OJessup/LightsaberAntimatter/DocsAndDiagrams/V2.0/Lightsaber [Antimatter] Block Diagram V2.0.jpeg

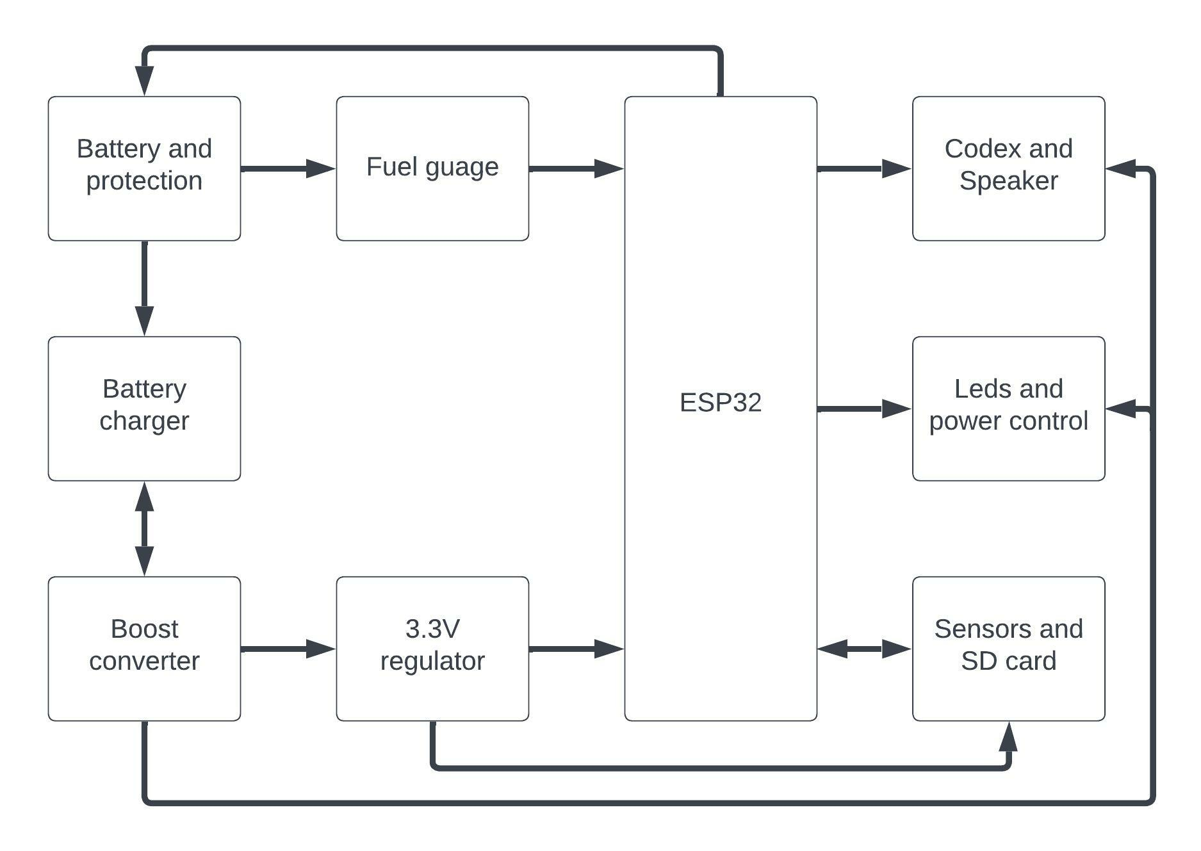
DocsAndDiagrams/V2.0/Lightsaber [Antimatter] Block Diagram V2.0.jpeg
