OJessup/LightsaberAntimatter/Inspiration/Copper and aluminium.jpeg

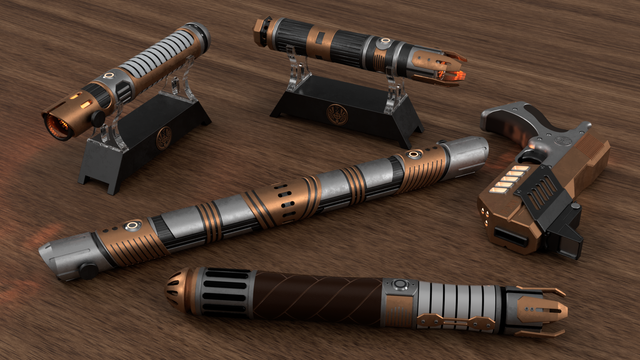
Inspiration/Copper and aluminium.jpeg
