OJessup/LightsaberAntimatter/Inspiration/Gold and Black.jpeg

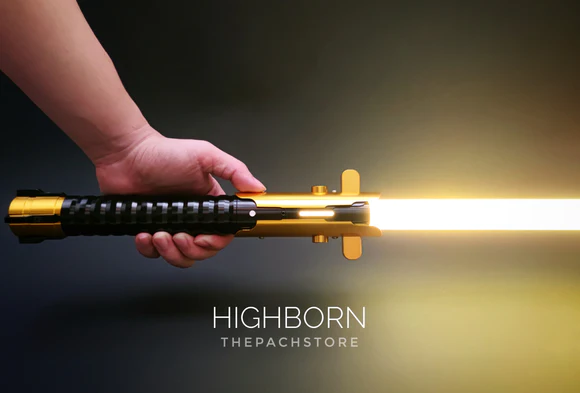
Inspiration/Gold and Black.jpeg
