OJessup/LightsaberAntimatter/Inspiration/Leather grip.jpeg

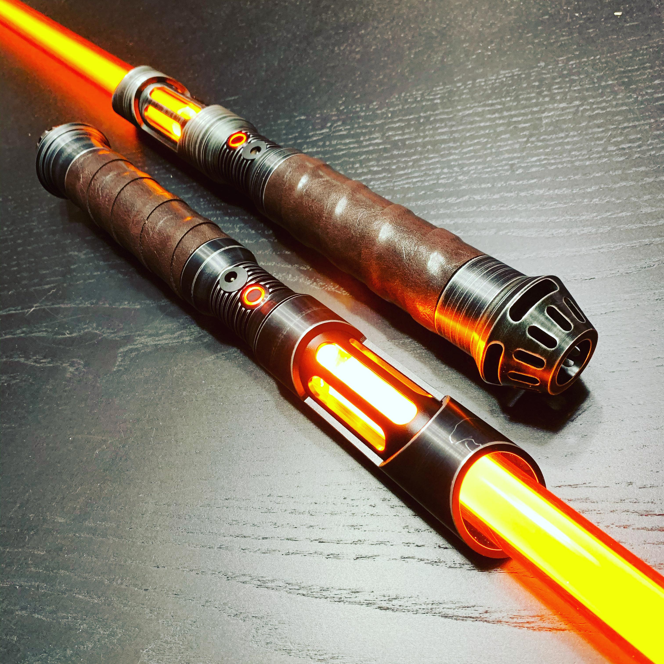
Inspiration/Leather grip.jpeg
