OJessup/LightsaberAntimatter/Inspiration/starkiller 1.jpeg

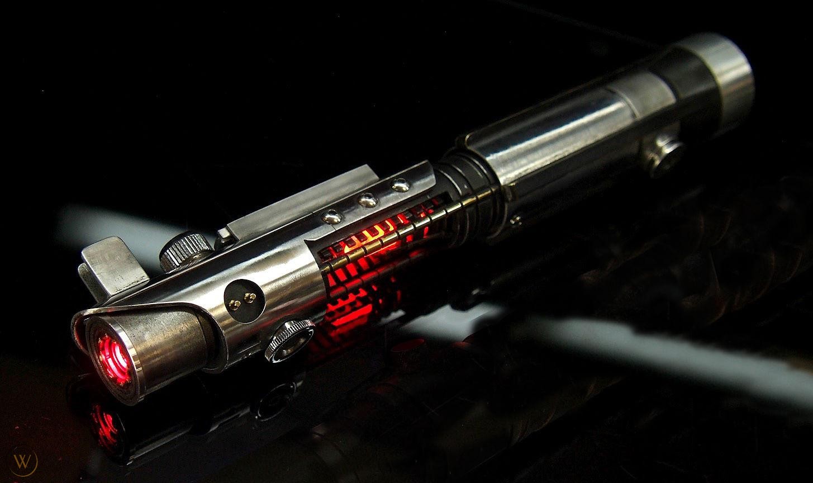
Inspiration/starkiller 1.jpeg
