OJessup/LightsaberAntimatter/Inspiration/starkiller 3.jpeg

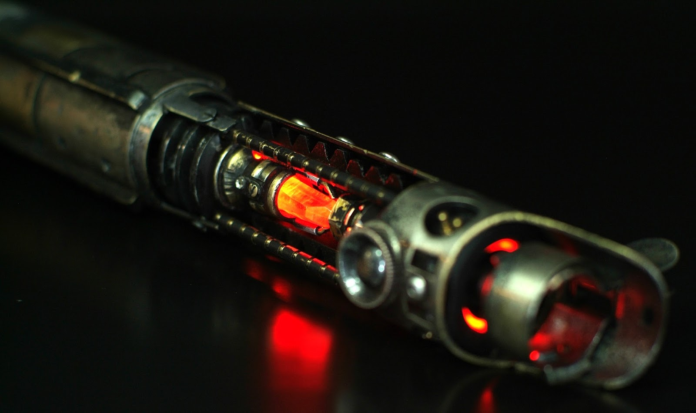
Inspiration/starkiller 3.jpeg
