OJessup/LightsaberAntimatter/Inspiration/starkiller 4.jpeg

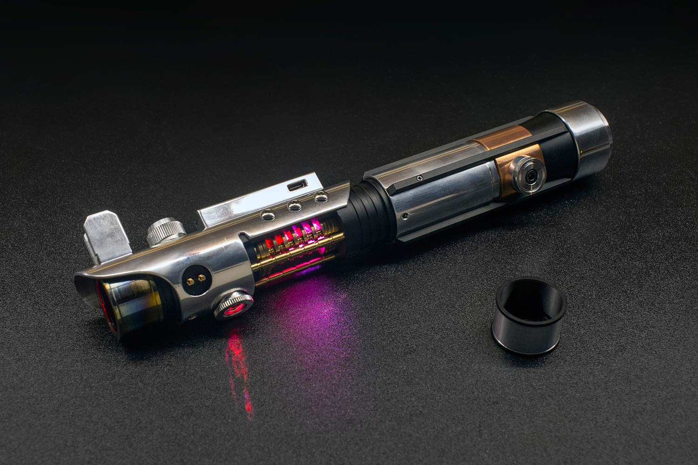
Inspiration/starkiller 4.jpeg
