OJessup/LightsaberAntimatter/ProgressDump/3A280642-E206-4C3E-A6EC-DA5A2EA1DF64.jpg

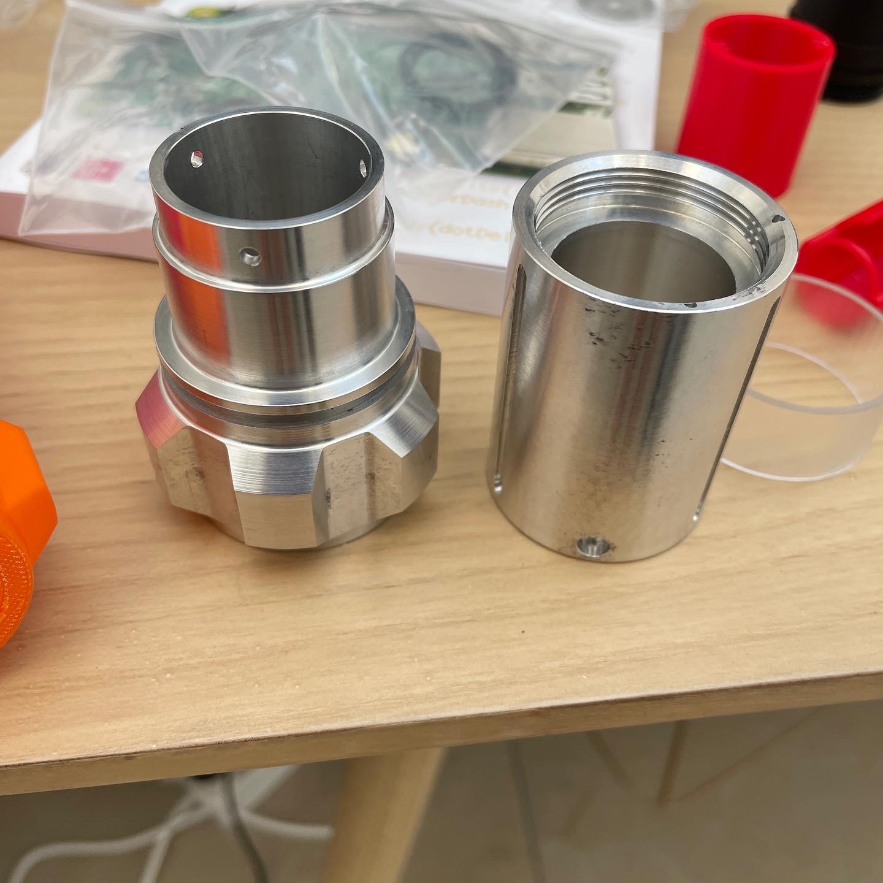
ProgressDump/3A280642-E206-4C3E-A6EC-DA5A2EA1DF64.jpg
