OJessup/LightsaberAntimatter/ProgressDump/76434946-092B-4D3E-A22C-4221BAEBB1AF.jpg

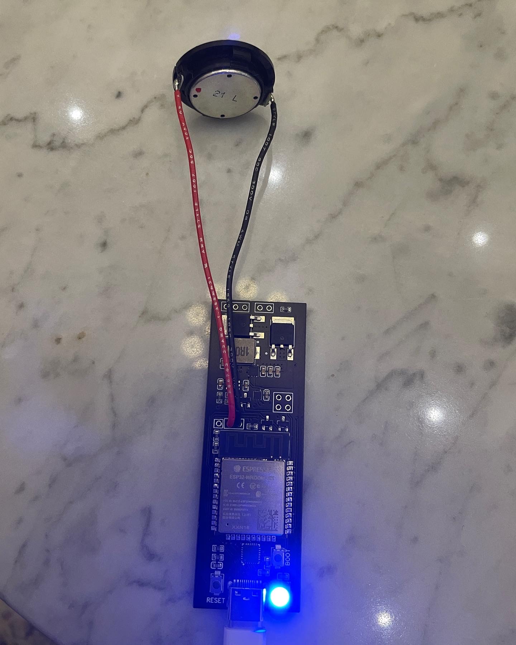
ProgressDump/76434946-092B-4D3E-A22C-4221BAEBB1AF.jpg
