OJessup/LightsaberAntimatter/ProgressDump/ABE4BEE7-62A8-4462-B97B-0894F94DCD76.jpg

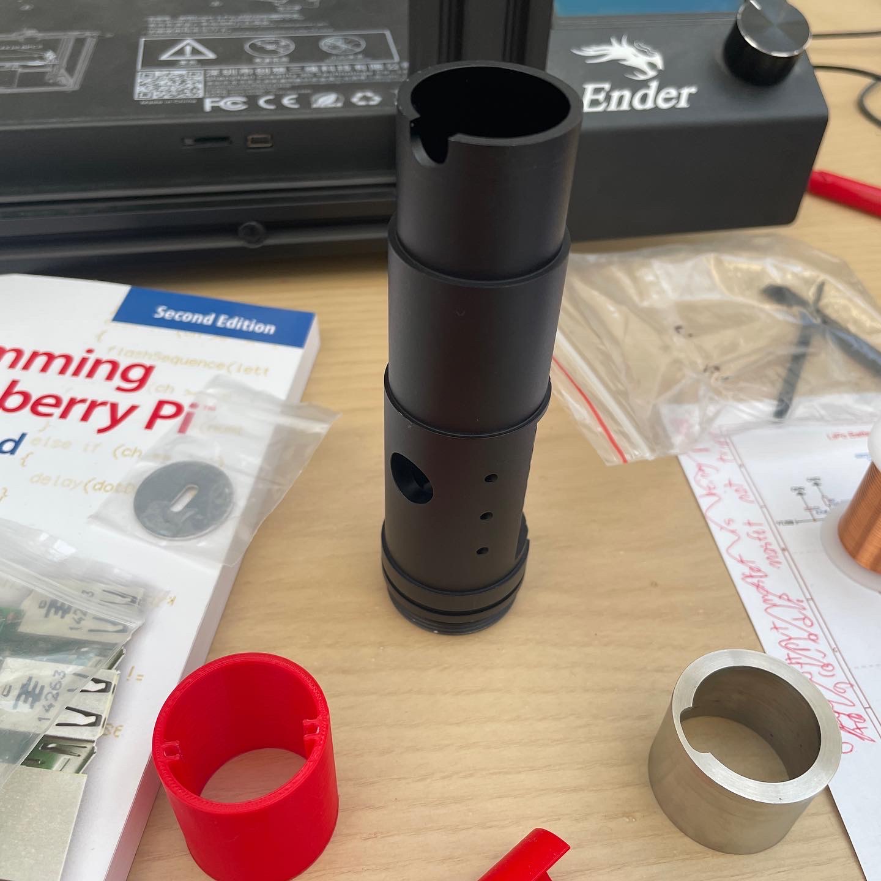
ProgressDump/ABE4BEE7-62A8-4462-B97B-0894F94DCD76.jpg
