OJessup/LightsaberAntimatter/ProgressDump/IMG_3394.JPG

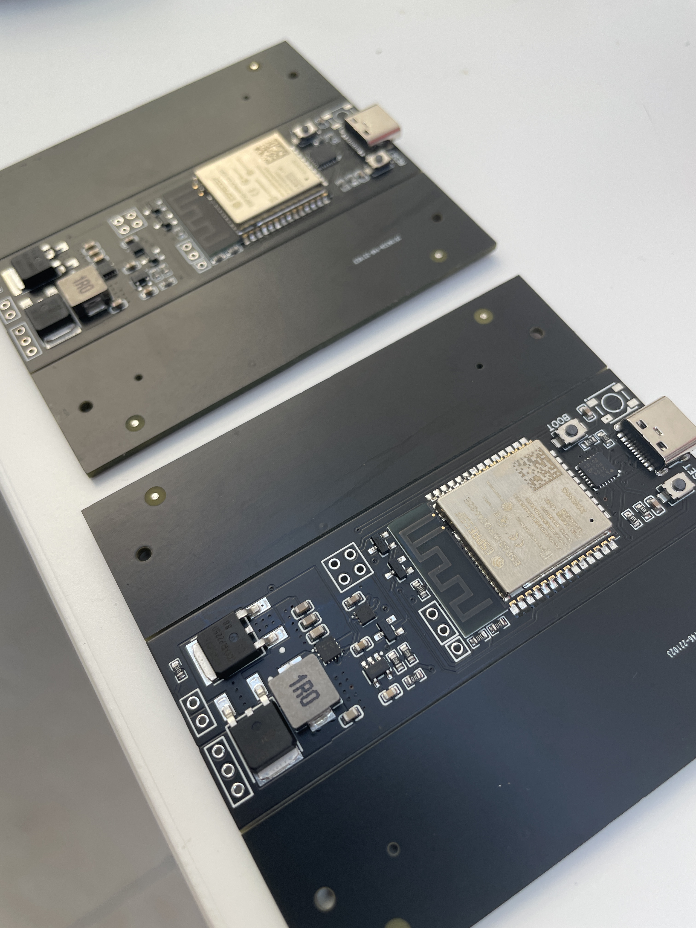
ProgressDump/IMG_3394.JPG
