OJessup/LightsaberAntimatter/ProgressDump/IMG_3398.JPG

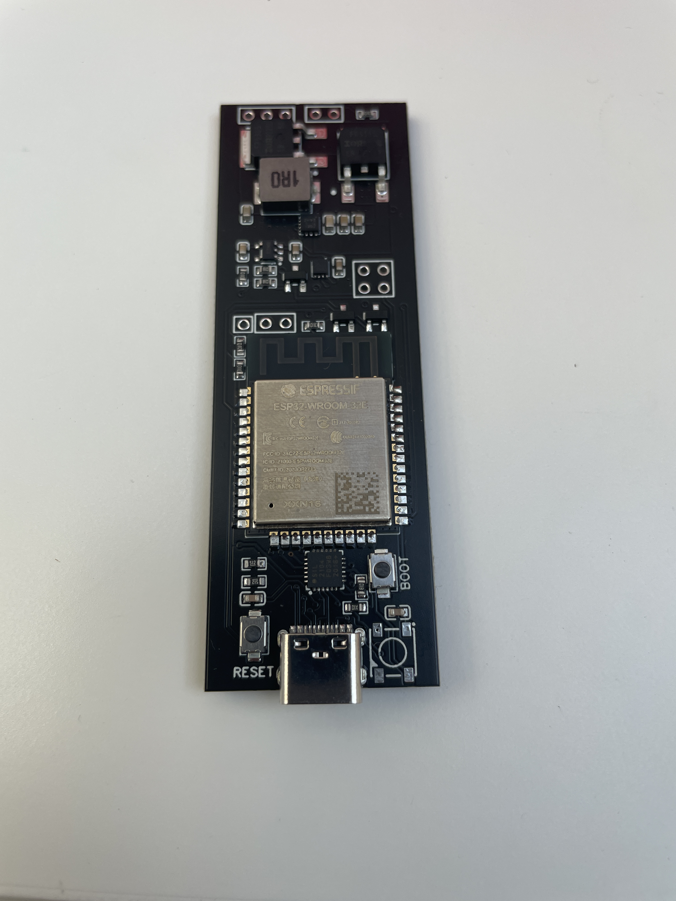
ProgressDump/IMG_3398.JPG
