OJessup/LightsaberAntimatter/ProgressDump/IMG_3399.JPG

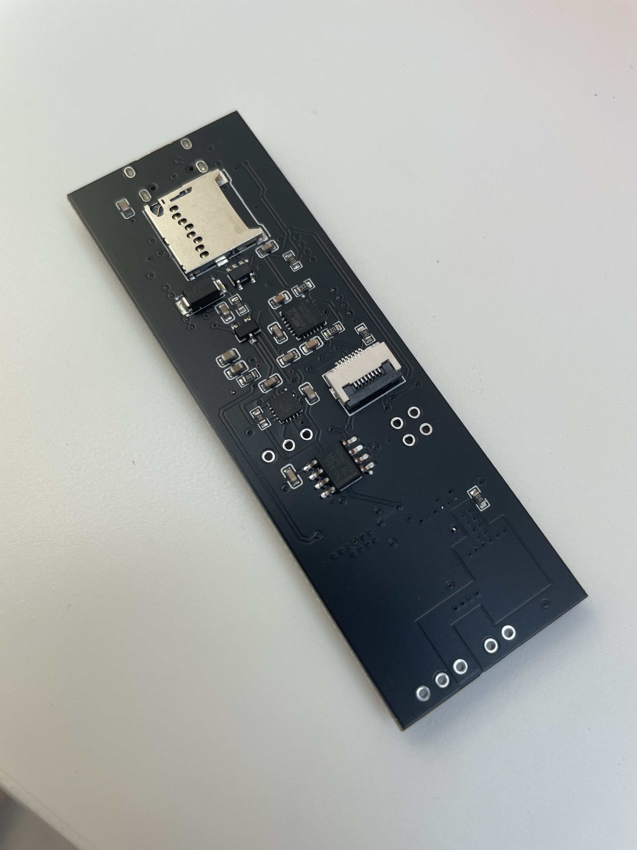
ProgressDump/IMG_3399.JPG
