OJessup/LightsaberAntimatter/ProgressDump/IMG_4058.JPG

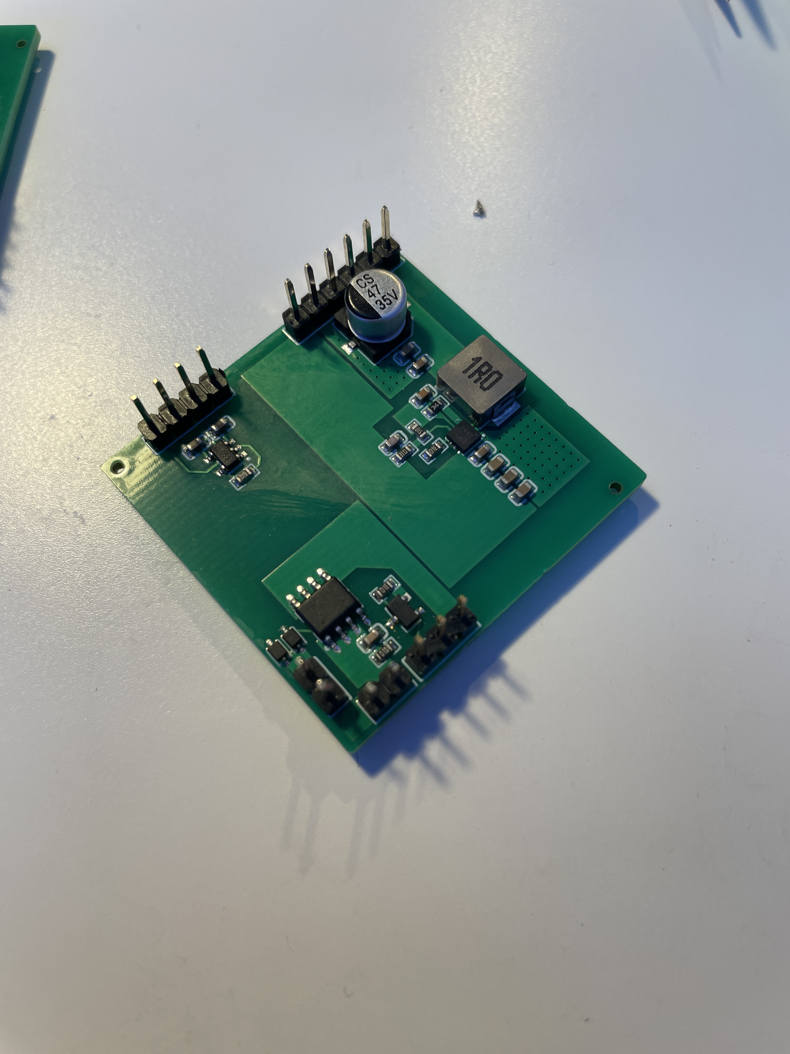
ProgressDump/IMG_4058.JPG
