OJessup/LightsaberAntimatter/ProgressDump/IMG_4652.JPG

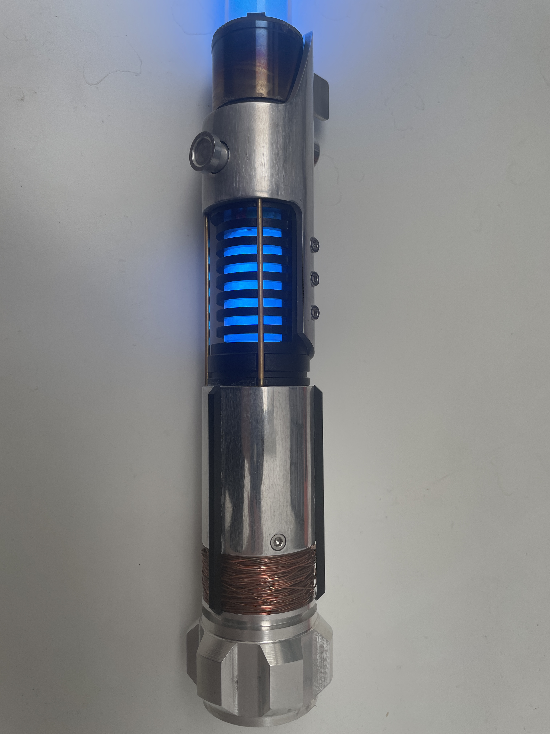
ProgressDump/IMG_4652.JPG
