OJessup/LightsaberAntimatter/CAD/STEP files/Underframe-01.step

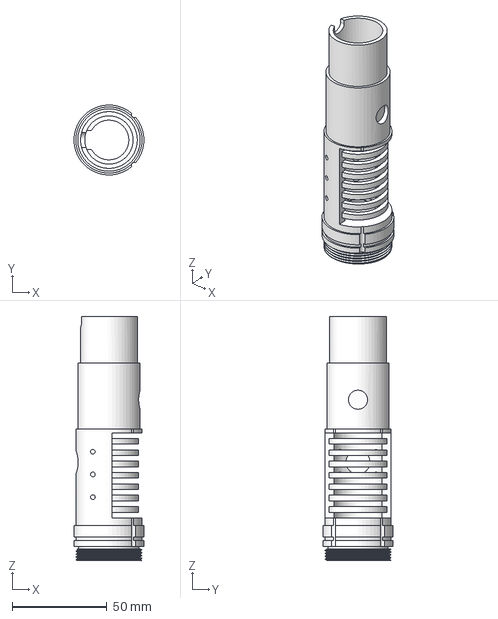
[picture p39: CAD file, 2022-11-18]
CAD/STEP files/Underframe-01.step
37.0 x 37.0 x 129.0 mm
