OJessup/LightsaberAntimatter/CAD/STEP files/EmitterCover-01.step

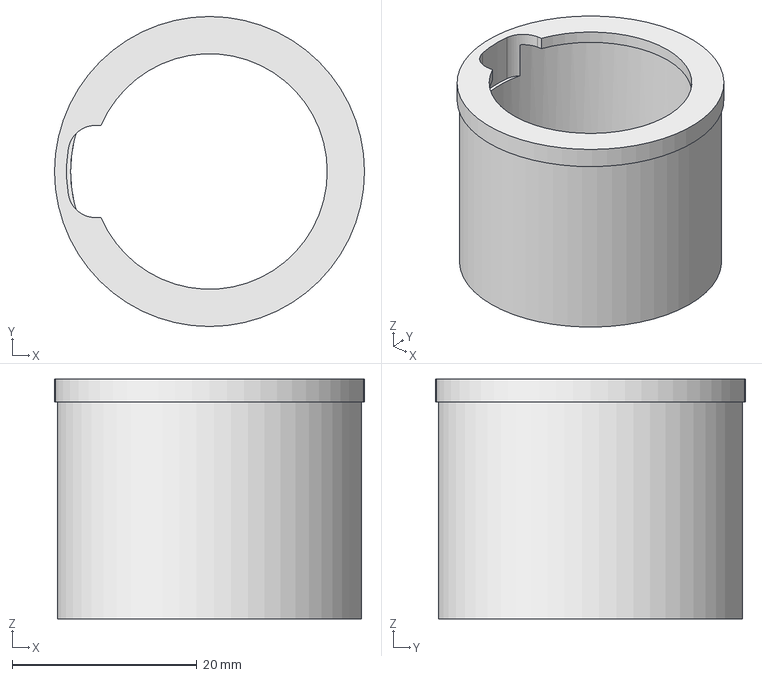
[picture p40: CAD file, 2022-11-18]
CAD/STEP files/EmitterCover-01.step
33.6 x 33.6 x 26.0 mm
