OJessup/LightsaberAntimatter/ProgressDump/IMG_3277.JPG

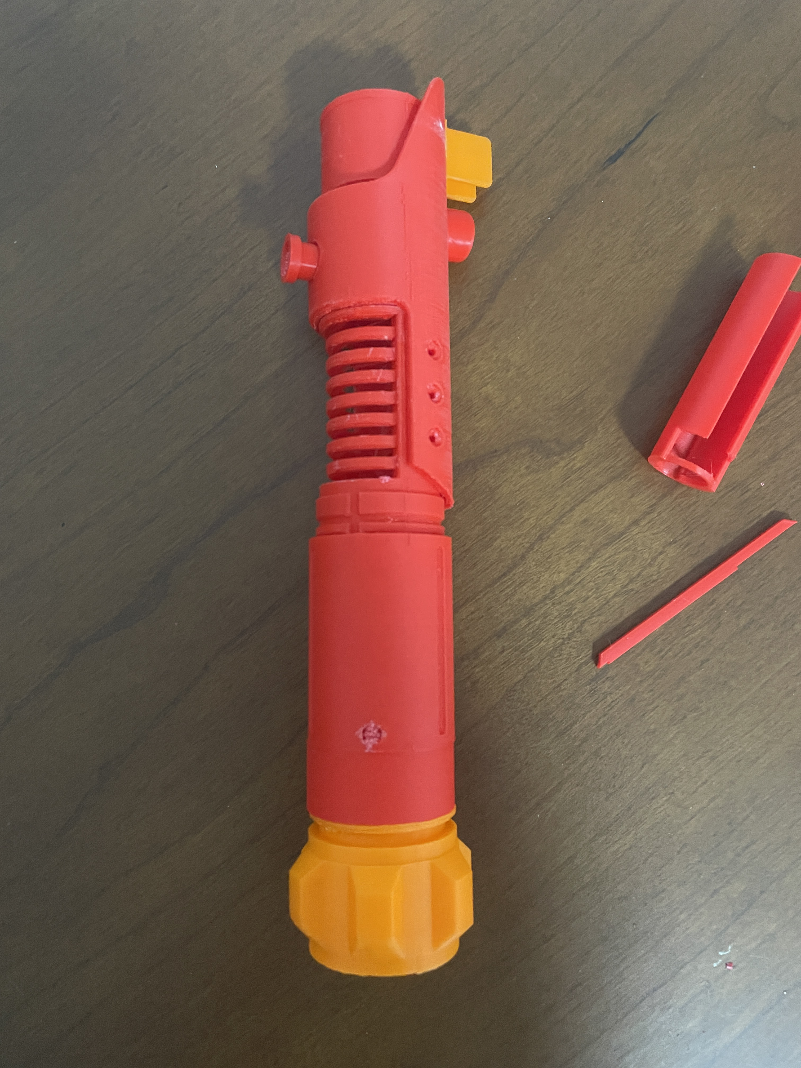
ProgressDump/IMG_3277.JPG
