OJessup/LightsaberAntimatter/ProgressDump/IMG_3279.JPG

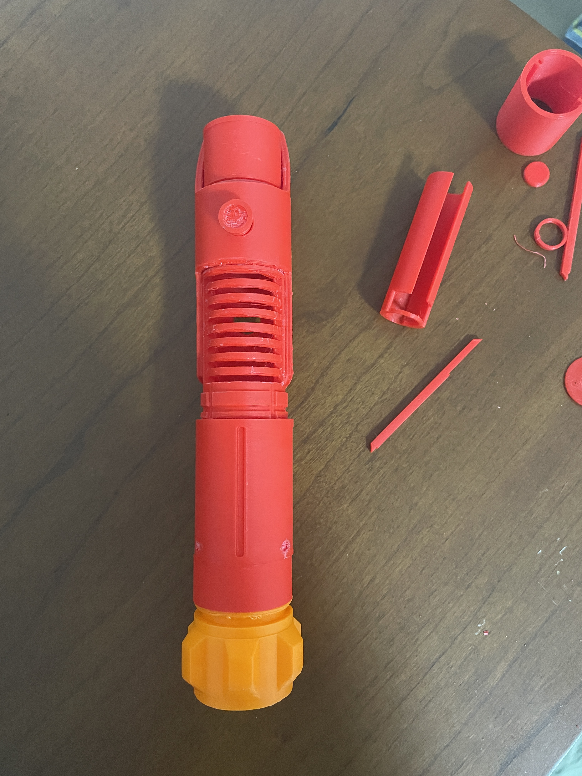
ProgressDump/IMG_3279.JPG
