OJessup/LightsaberAntimatter/ProgressDump/IMG_3930.JPG

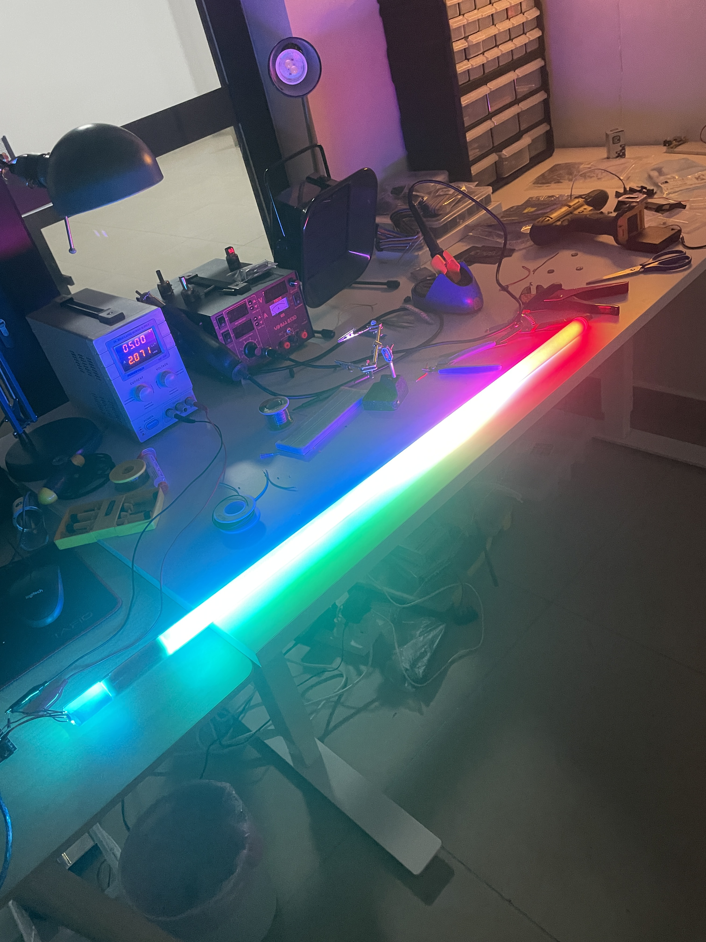
ProgressDump/IMG_3930.JPG
