OJessup/LightsaberAntimatter/ProgressDump/IMG_3598.JPG

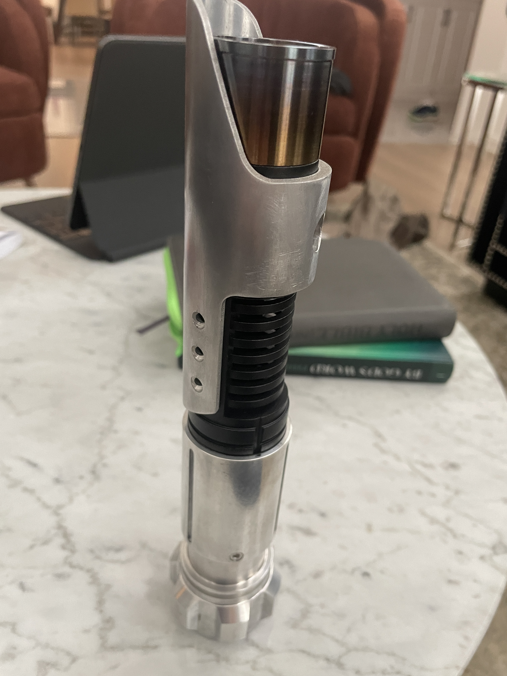
ProgressDump/IMG_3598.JPG
